malkam03/Pianoduino/Datasheets/4x4-schem.png

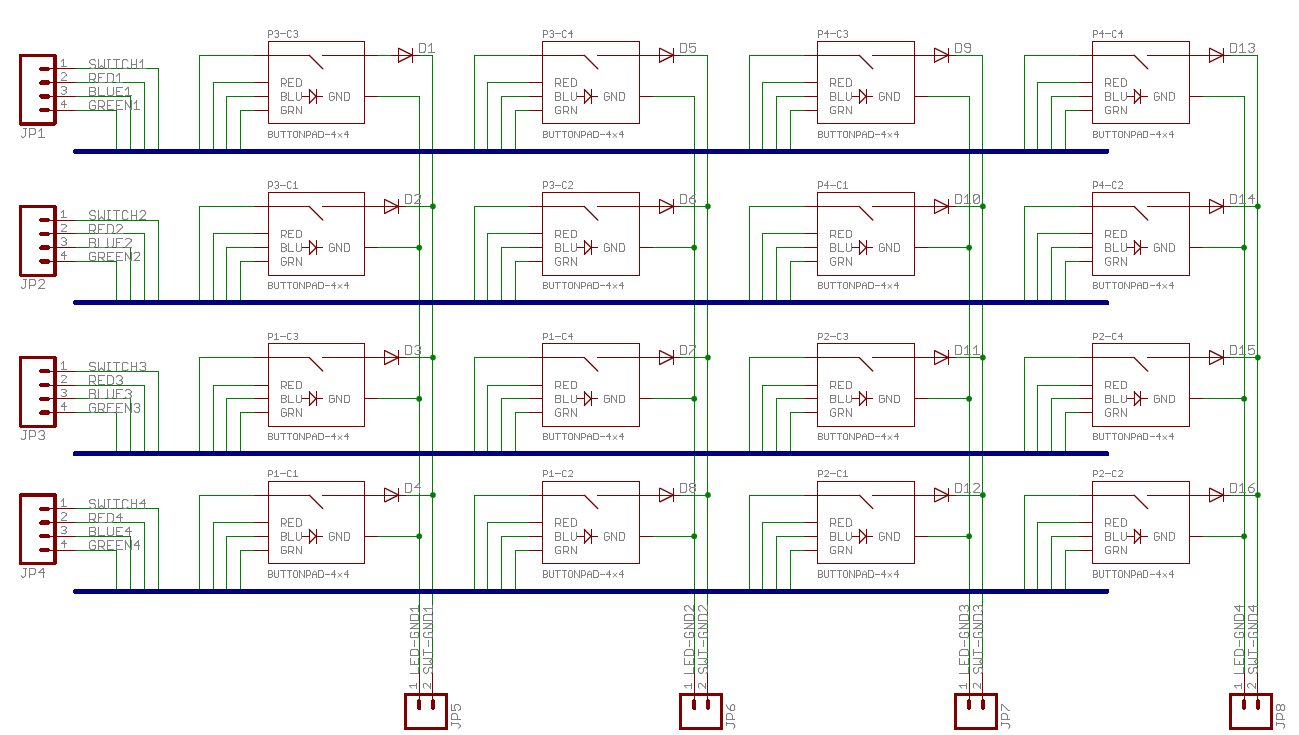
Datasheets/4x4-schem.png
