malkam03/Pianoduino/Datasheets/A-853.jpg

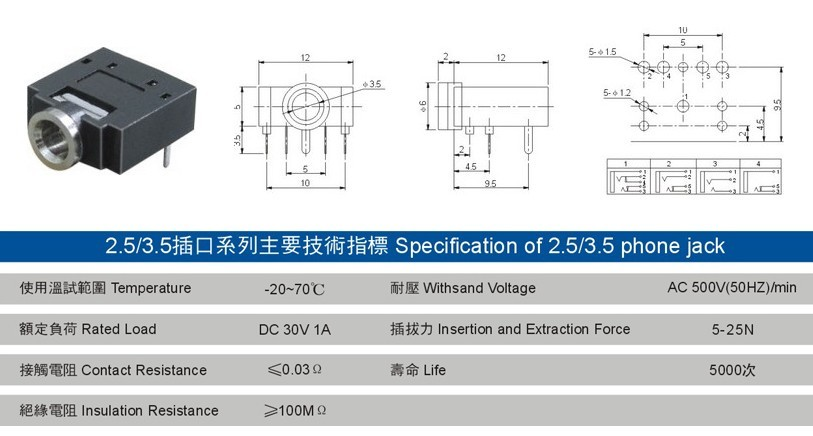
Datasheets/A-853.jpg
