malkam03/Pianoduino/Renderings/Animation/Pianoduinojpg0009.jpg

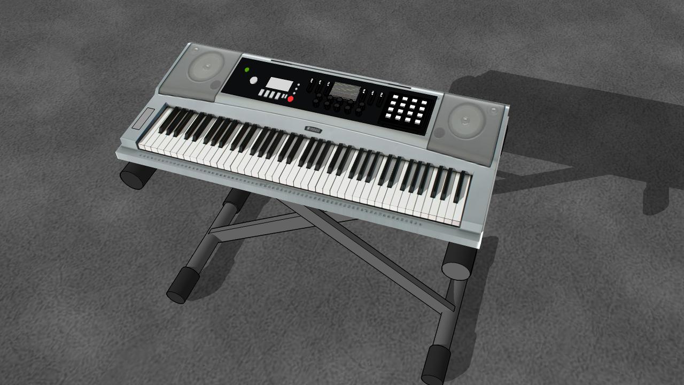
Renderings/Animation/Pianoduinojpg0009.jpg
