malkam03/Pianoduino/Renderings/Animation/Pianoduinojpg0015.jpg

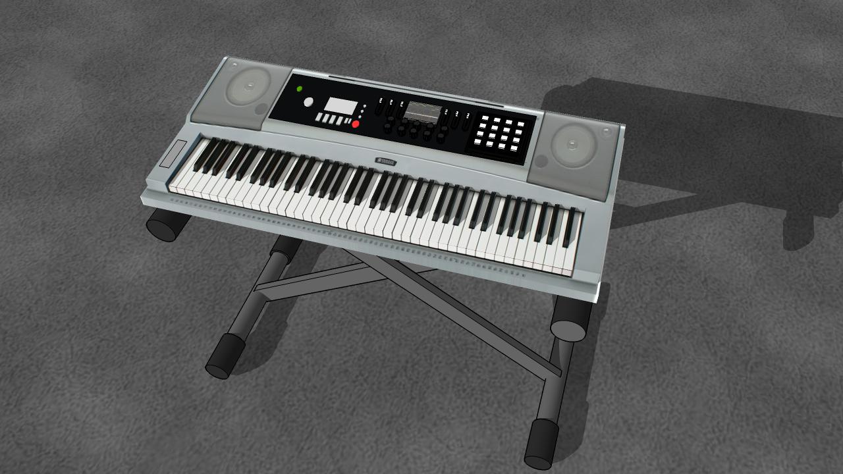
Renderings/Animation/Pianoduinojpg0015.jpg
