malkam03/Pianoduino/Renderings/Animation/Pianoduinojpg0021.jpg

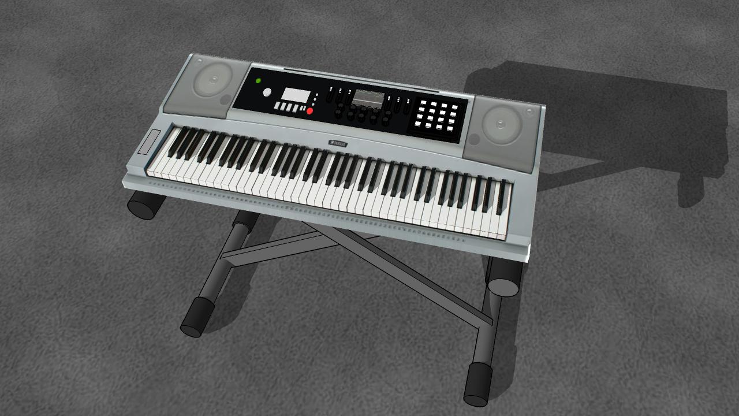
Renderings/Animation/Pianoduinojpg0021.jpg
