malkam03/Pianoduino/Renderings/Animation/Pianoduinojpg0022.jpg

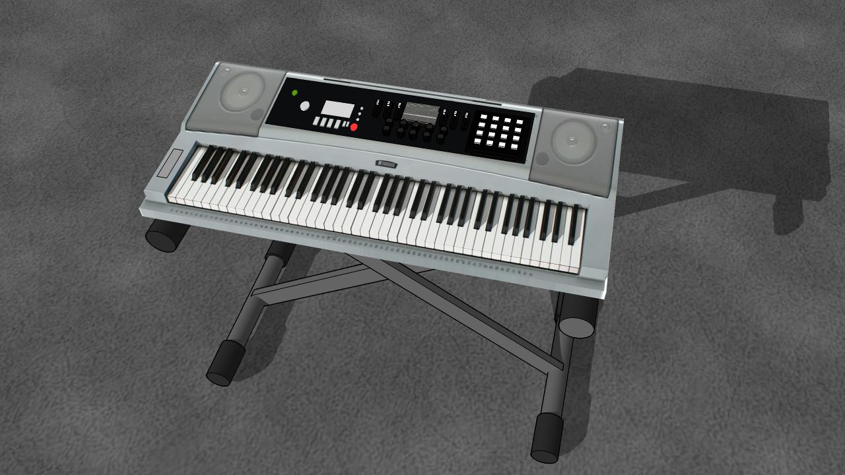
Renderings/Animation/Pianoduinojpg0022.jpg
