malkam03/Pianoduino/Renderings/Animation/Pianoduinojpg0029.jpg

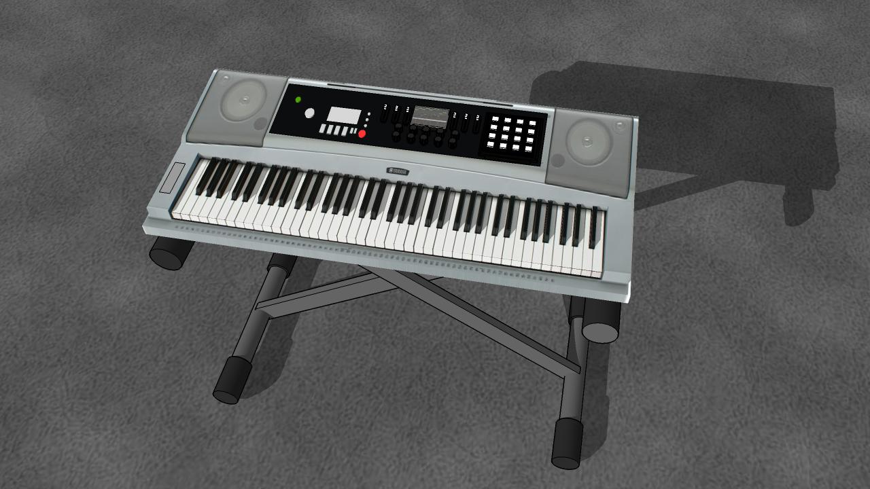
Renderings/Animation/Pianoduinojpg0029.jpg
