malkam03/Pianoduino/Renderings/Animation/Pianoduinojpg0036.jpg

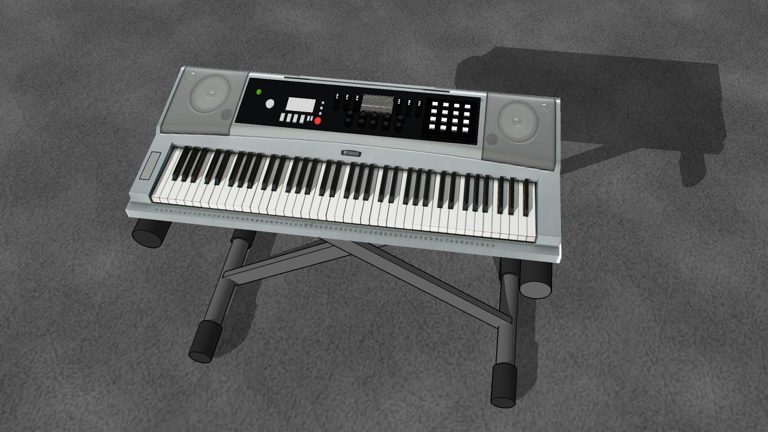
Renderings/Animation/Pianoduinojpg0036.jpg
