malkam03/Pianoduino/Renderings/Animation/Pianoduinojpg0039.jpg

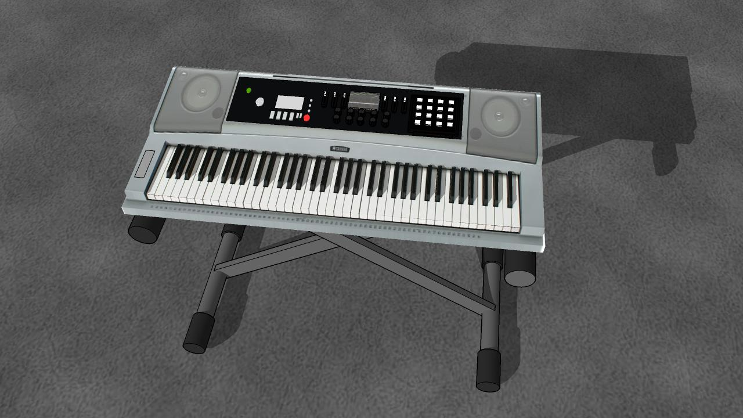
Renderings/Animation/Pianoduinojpg0039.jpg
