malkam03/Pianoduino/Renderings/Animation/Pianoduinojpg0041.jpg

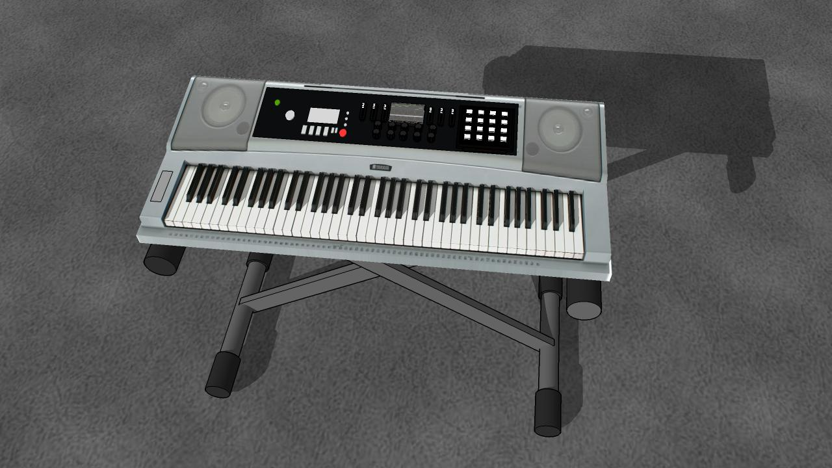
Renderings/Animation/Pianoduinojpg0041.jpg
