malkam03/Pianoduino/Renderings/Animation/Pianoduinojpg0043.jpg

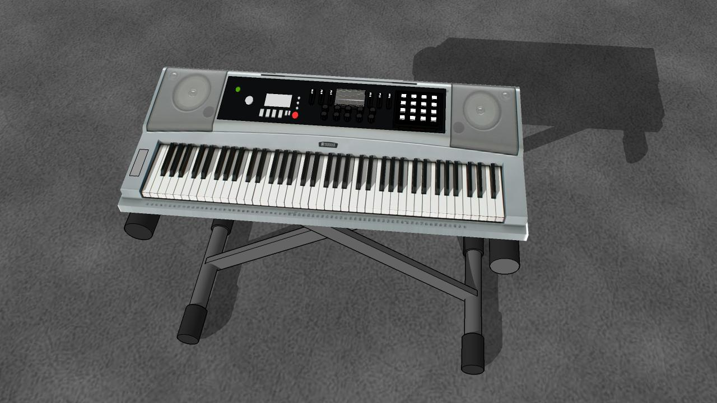
Renderings/Animation/Pianoduinojpg0043.jpg
