malkam03/Pianoduino/Renderings/Animation/Pianoduinojpg0049.jpg

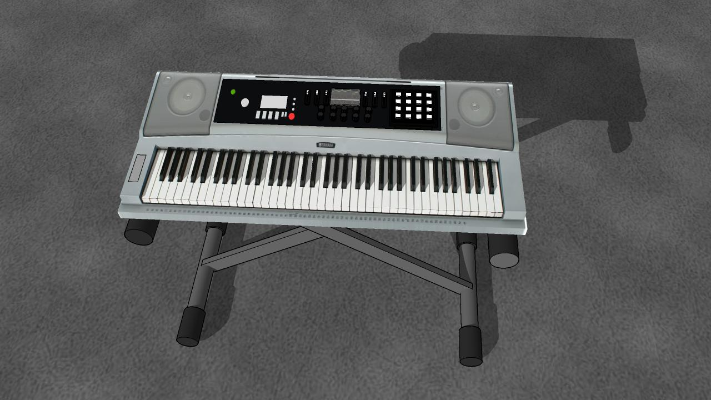
Renderings/Animation/Pianoduinojpg0049.jpg
