malkam03/Pianoduino/Renderings/Animation/Pianoduinojpg0051.jpg

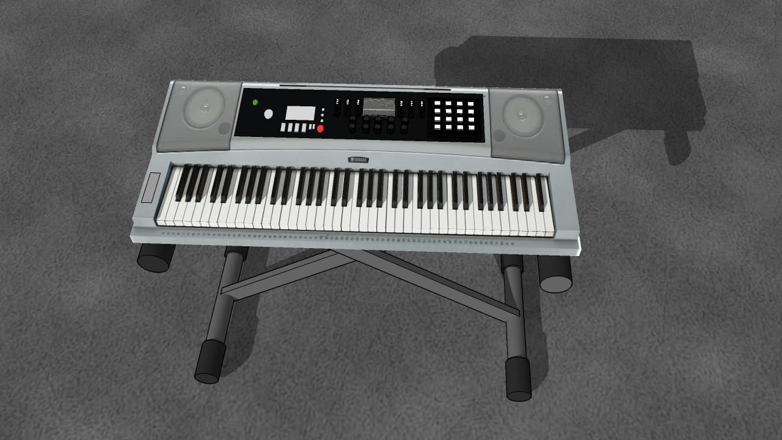
Renderings/Animation/Pianoduinojpg0051.jpg
