malkam03/Pianoduino/Renderings/Animation/Pianoduinojpg0054.jpg

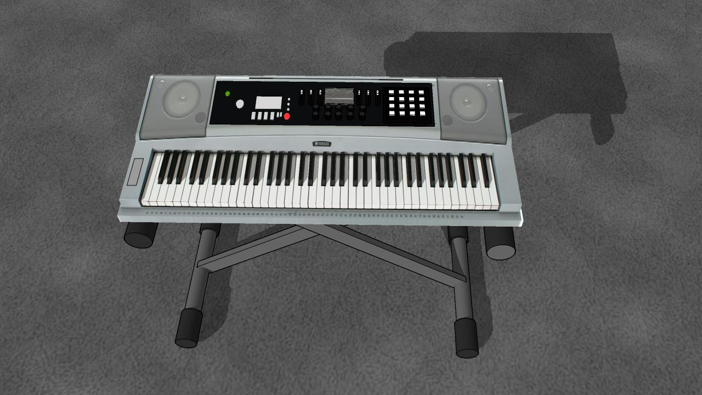
Renderings/Animation/Pianoduinojpg0054.jpg
