malkam03/Pianoduino/Renderings/Animation/Pianoduinojpg0057.jpg

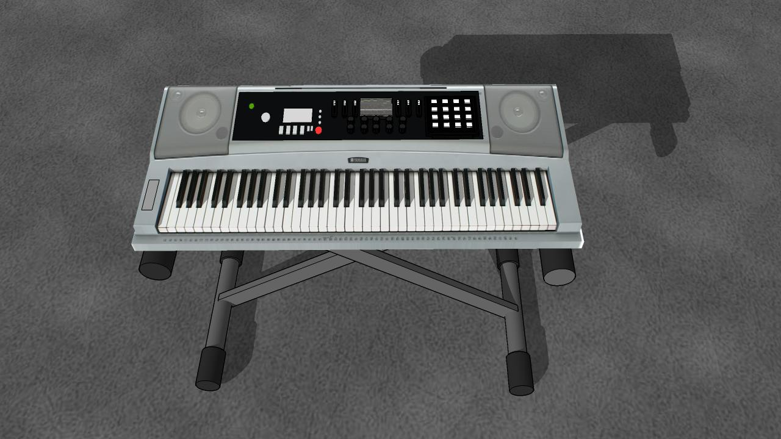
Renderings/Animation/Pianoduinojpg0057.jpg
