malkam03/Pianoduino/Renderings/Animation/Pianoduinojpg0059.jpg

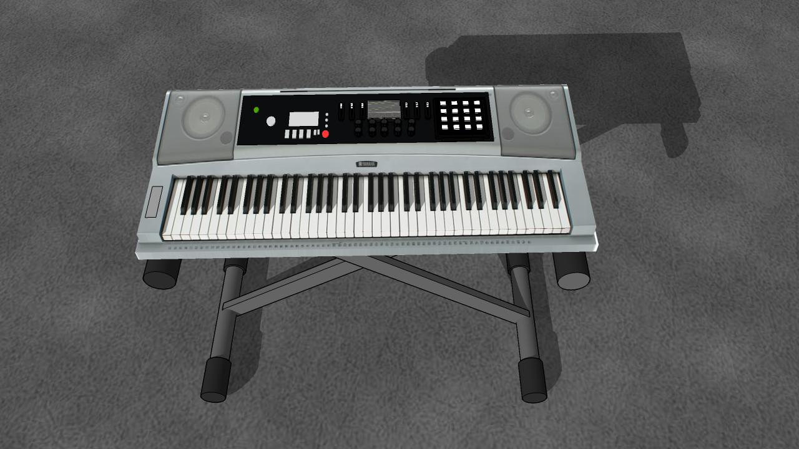
Renderings/Animation/Pianoduinojpg0059.jpg
