malkam03/Pianoduino/Renderings/Animation/Pianoduinojpg0060.jpg

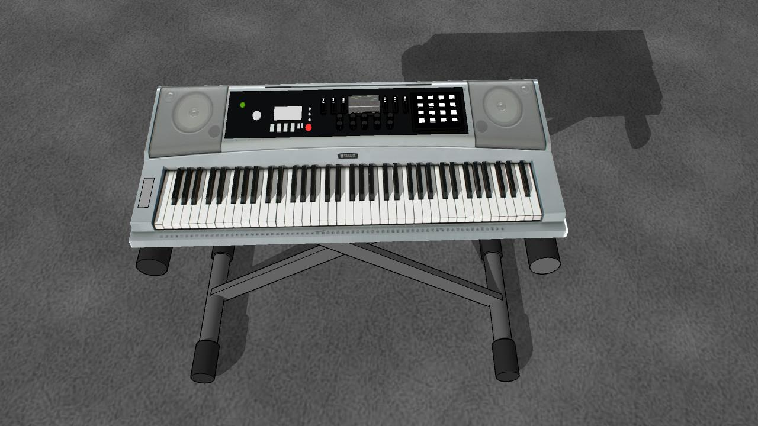
Renderings/Animation/Pianoduinojpg0060.jpg
