malkam03/Pianoduino/Renderings/Animation/Pianoduinojpg0063.jpg

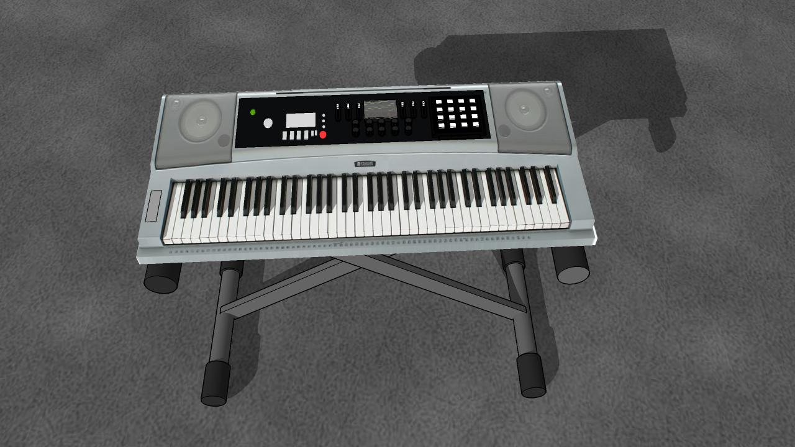
Renderings/Animation/Pianoduinojpg0063.jpg
