malkam03/Pianoduino/Renderings/Animation/Pianoduinojpg0076.jpg

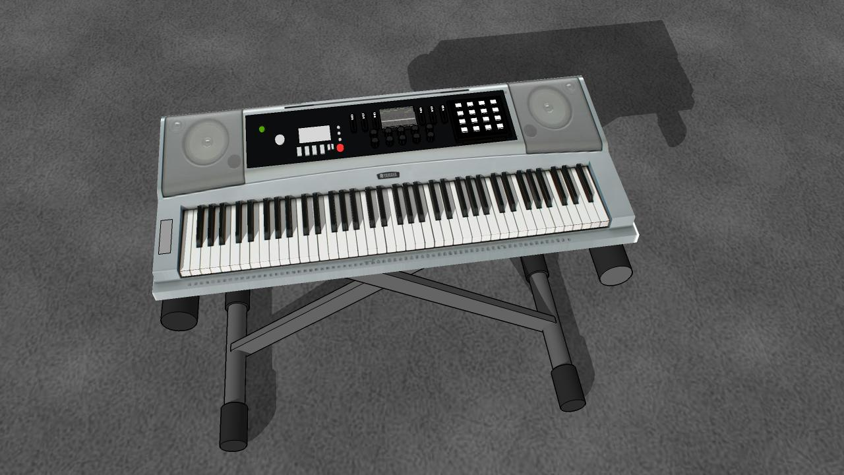
Renderings/Animation/Pianoduinojpg0076.jpg
