malkam03/Pianoduino/Renderings/Animation/Pianoduinojpg0081.jpg

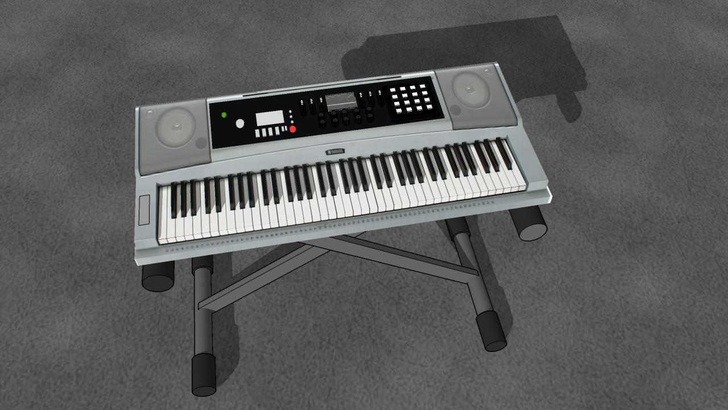
Renderings/Animation/Pianoduinojpg0081.jpg
