malkam03/Pianoduino/Renderings/Animation/Pianoduinojpg0087.jpg

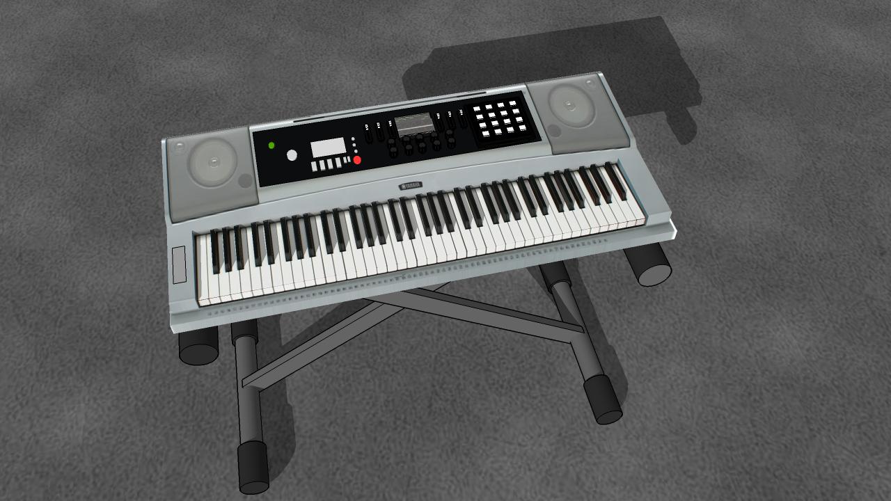
Renderings/Animation/Pianoduinojpg0087.jpg
