malkam03/Pianoduino/Renderings/Animation/Pianoduinojpg0091.jpg

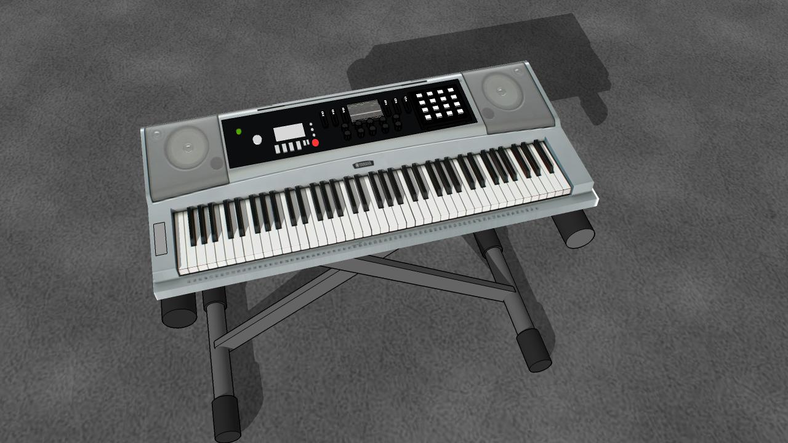
Renderings/Animation/Pianoduinojpg0091.jpg
