malkam03/Pianoduino/Renderings/Animation/Pianoduinojpg0093.jpg

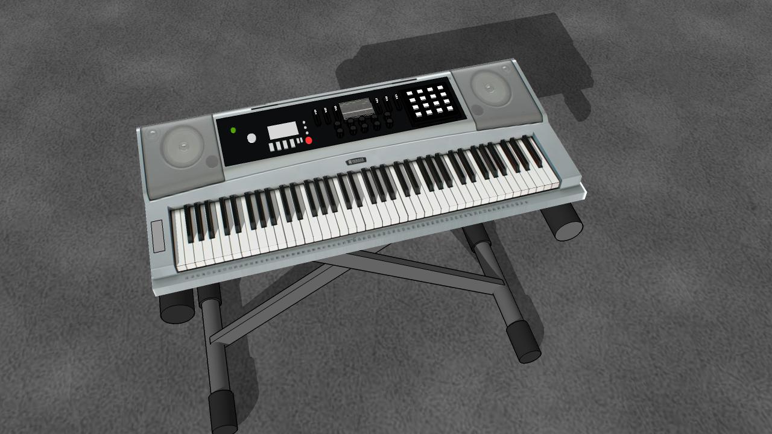
Renderings/Animation/Pianoduinojpg0093.jpg
