malkam03/Pianoduino/Renderings/Animation/Pianoduinojpg0097.jpg

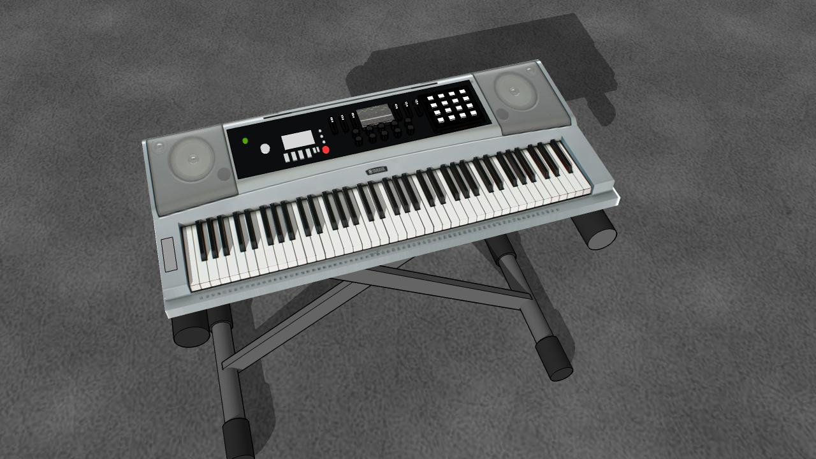
Renderings/Animation/Pianoduinojpg0097.jpg
