malkam03/Pianoduino/Renderings/Animation/Pianoduinojpg0109.jpg

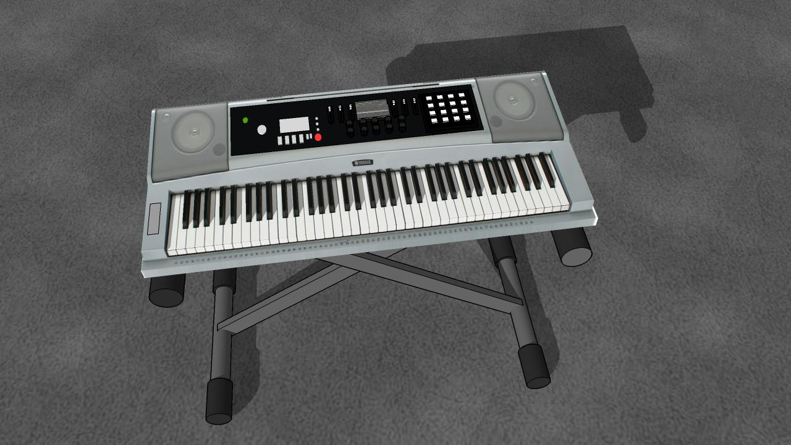
Renderings/Animation/Pianoduinojpg0109.jpg
