malkam03/Pianoduino/Renderings/Animation/Pianoduinojpg0117.jpg

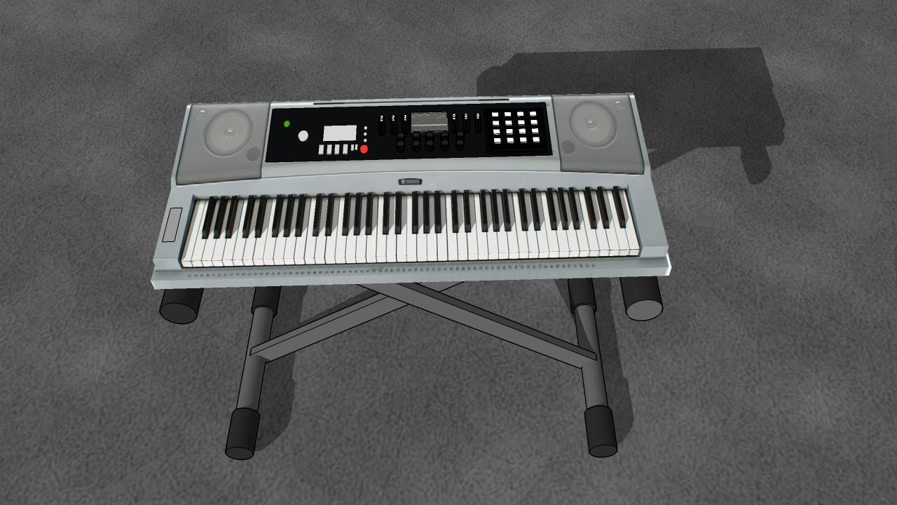
Renderings/Animation/Pianoduinojpg0117.jpg
