malkam03/Pianoduino/Renderings/Animation/Pianoduinojpg0118.jpg

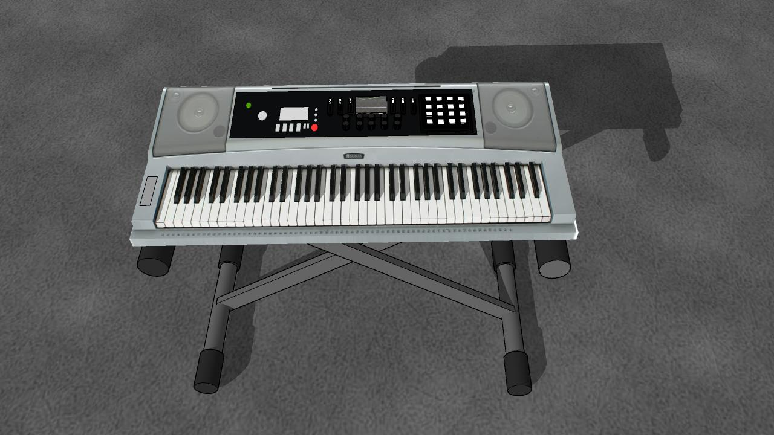
Renderings/Animation/Pianoduinojpg0118.jpg
