malkam03/Pianoduino/Renderings/Animation/Pianoduinojpg0121.jpg

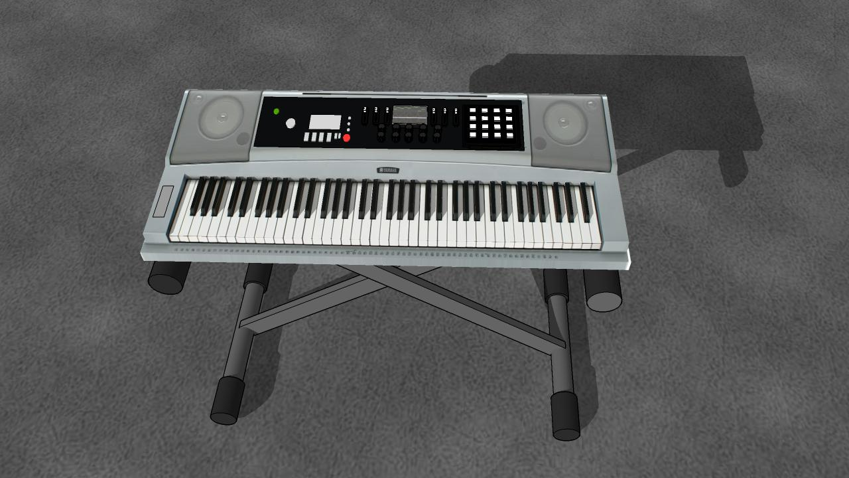
Renderings/Animation/Pianoduinojpg0121.jpg
