malkam03/Pianoduino/Renderings/Animation/Pianoduinojpg0122.jpg

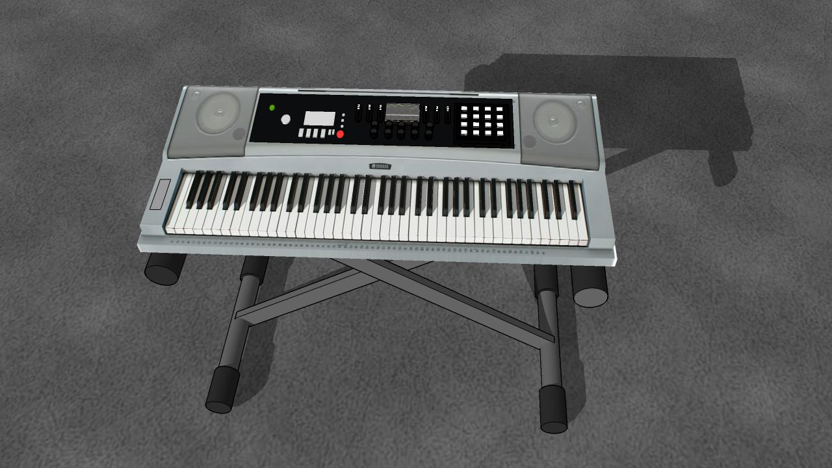
Renderings/Animation/Pianoduinojpg0122.jpg
