malkam03/Pianoduino/Renderings/Animation/Pianoduinojpg0124.jpg

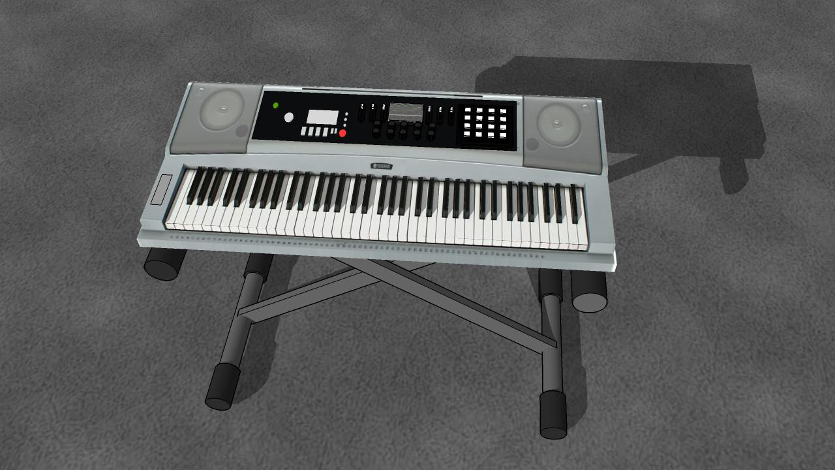
Renderings/Animation/Pianoduinojpg0124.jpg
