malkam03/Pianoduino/Renderings/Animation/Pianoduinojpg0127.jpg

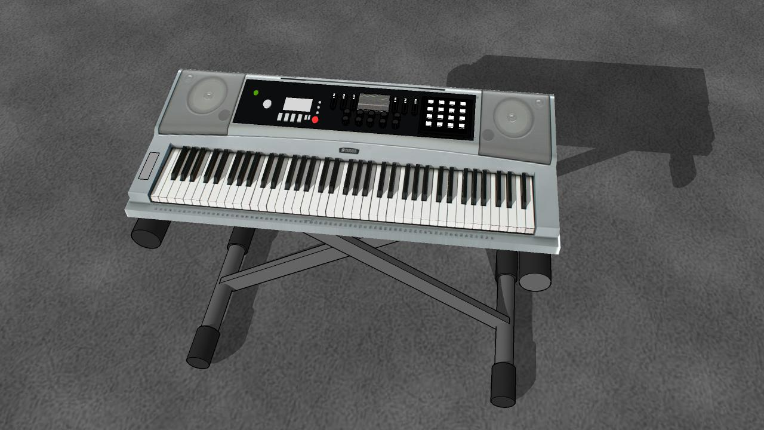
Renderings/Animation/Pianoduinojpg0127.jpg
