malkam03/Pianoduino/Renderings/Animation/Pianoduinojpg0130.jpg

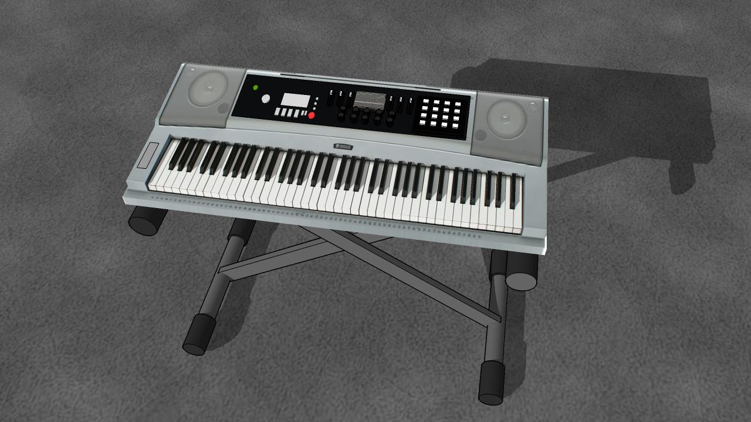
Renderings/Animation/Pianoduinojpg0130.jpg
