malkam03/Pianoduino/Renderings/Animation/Pianoduinojpg0132.jpg

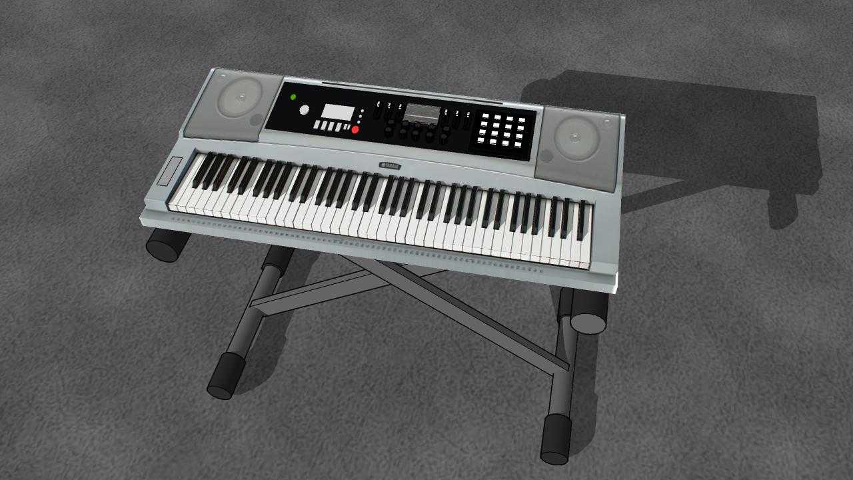
Renderings/Animation/Pianoduinojpg0132.jpg
