malkam03/Pianoduino/Renderings/Animation/Pianoduinojpg0141.jpg

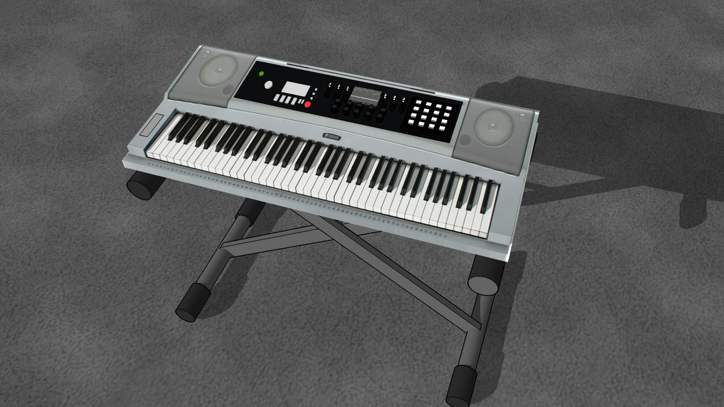
Renderings/Animation/Pianoduinojpg0141.jpg
