malkam03/Pianoduino/Renderings/Option 1.jpg

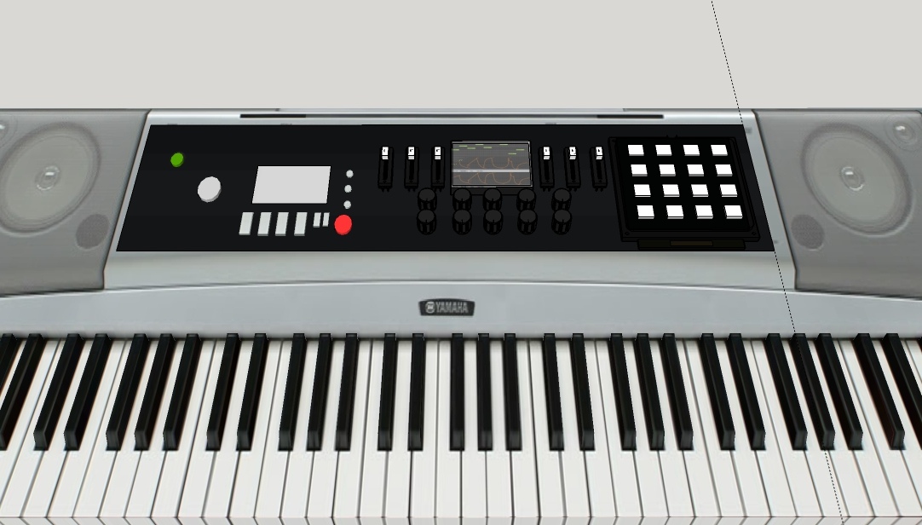
Renderings/Option 1.jpg
